DIYSynthMNL/Eurorack-Electric-Druid-VCDO1/kicad/Eurorack_Electric_Druid_VCDO1_Control_Board.kicad_sch

## KiCad design kicad/Eurorack_Electric_Druid_VCDO1_Control_Board.kicad_sch (2025-03-11, an earlier design)

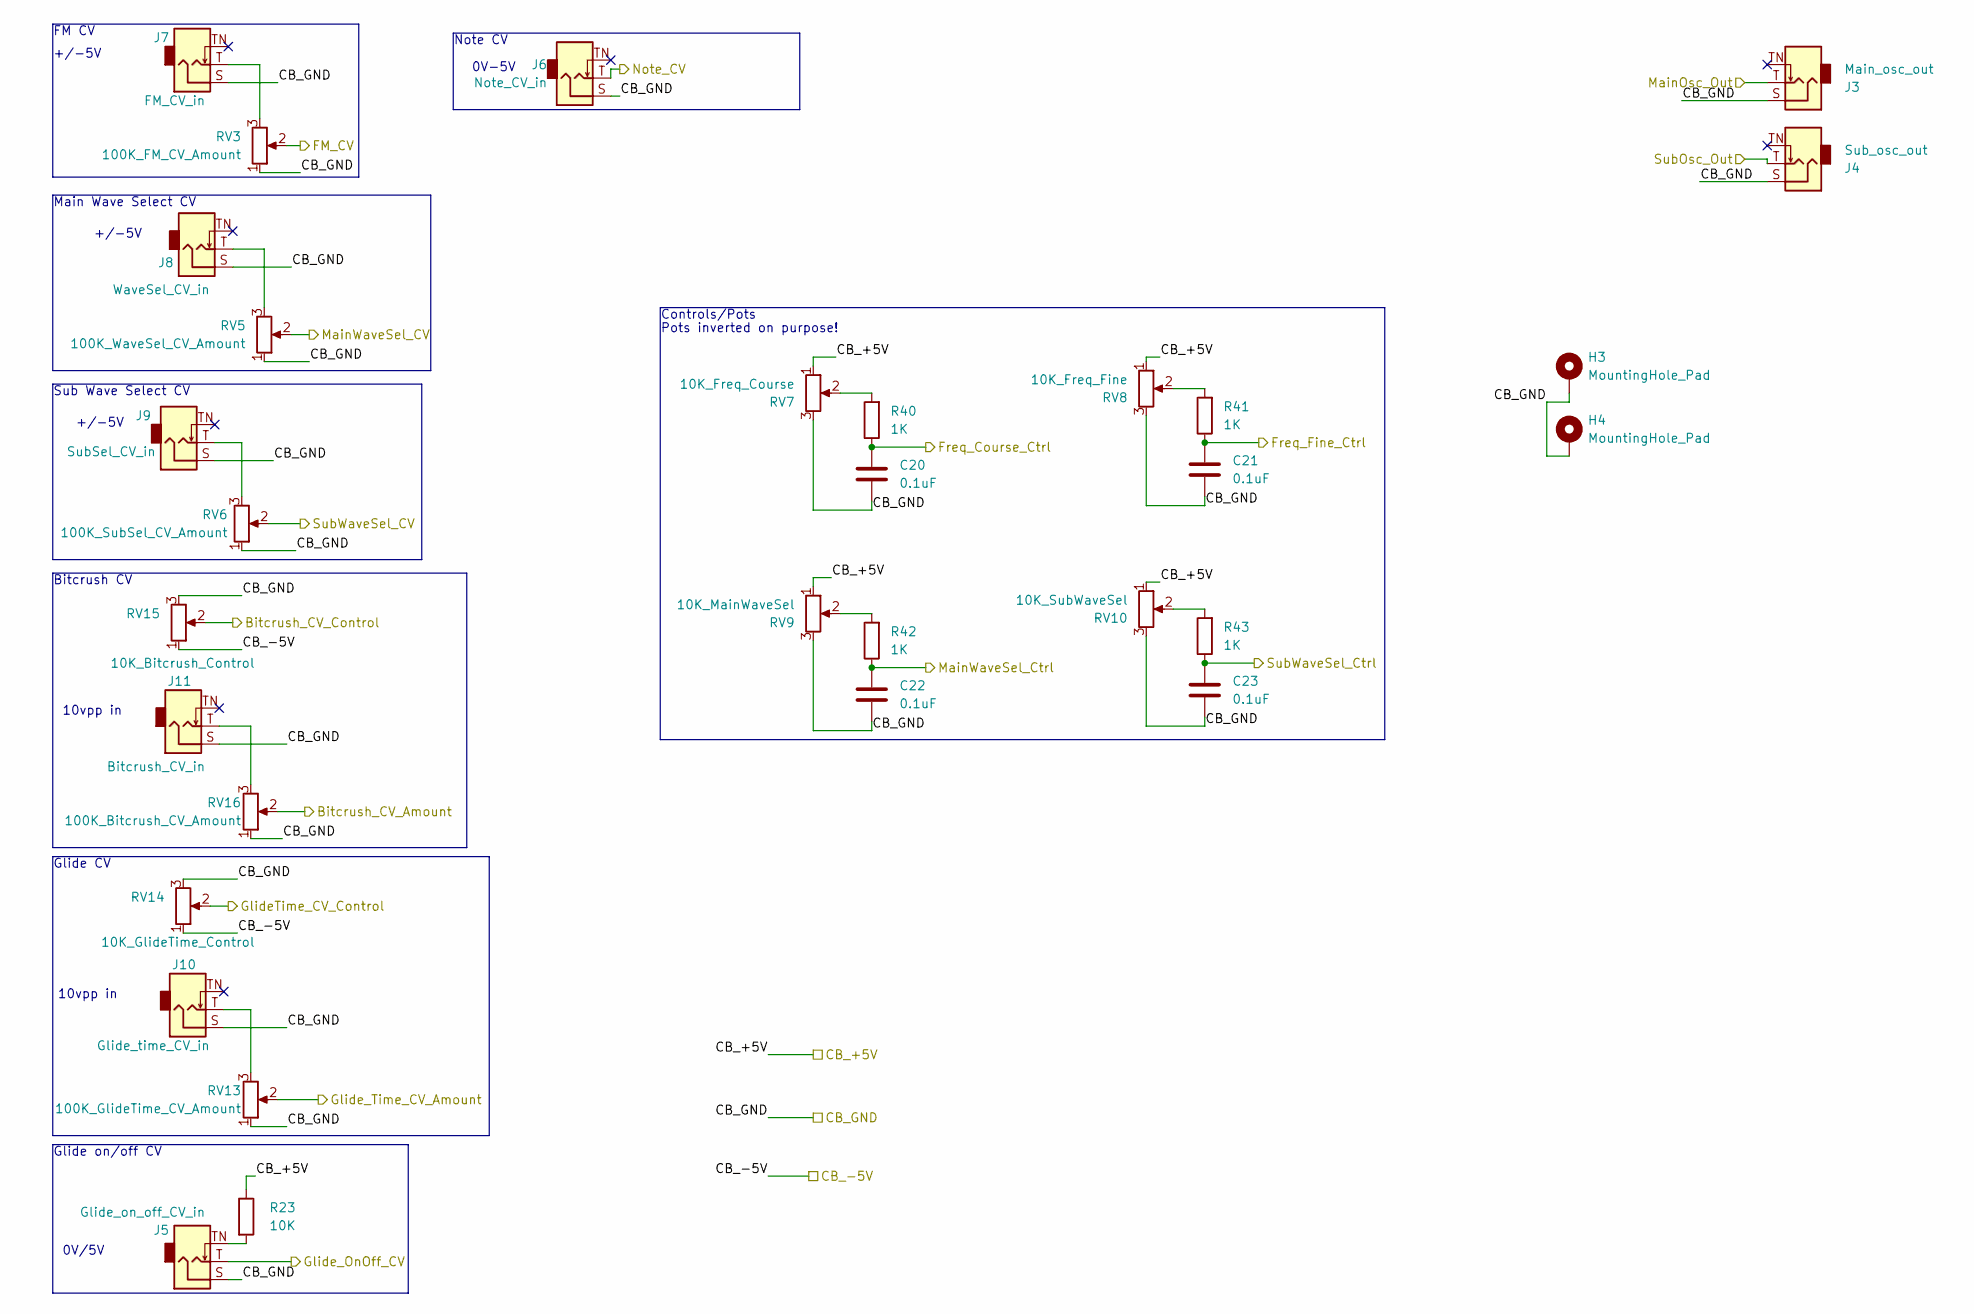
[picture p33: schematic Eurorack_Electric_Druid_VCDO1_Control_Board.kicad_sch]

Parts:
C20, C21, C22, C23: 0.1uF; C_Rect_L7.0mm_W2.0mm_P5.00mm_BigPads
H3, H4: MountingHole_Pad; MountingHole_M3_Standoff_Pad
J3: Main_osc_out; AudioJack_3.5mm_long_pads
J4: Sub_osc_out; AudioJack_3.5mm_long_pads
J5: Glide_on_off_CV_in; AudioJack_3.5mm_long_pads
J6: Note_CV_in; AudioJack_3.5mm_long_pads
J7: FM_CV_in; AudioJack_3.5mm_long_pads
J8: WaveSel_CV_in; AudioJack_3.5mm_long_pads
J9: SubSel_CV_in; AudioJack_3.5mm_long_pads
J10: Glide_time_CV_in; AudioJack_3.5mm_long_pads
J11: Bitcrush_CV_in; AudioJack_3.5mm_long_pads
R23: 10K; R_quarter_watt_L6.3mm_D2.5mm_P7.62mm
R40, R41, R42, R43: 1K; R_quarter_watt_L6.3mm_D2.5mm_P7.62mm
RV3: 100K_FM_CV_Amount; Potentiometer_RV09_BigPads
RV5: 100K_WaveSel_CV_Amount; Potentiometer_RV09_BigPads
RV6: 100K_SubSel_CV_Amount; Potentiometer_RV09_BigPads
RV7: 10K_Freq_Course; Potentiometer_RV09_BigPads
RV8: 10K_Freq_Fine; Potentiometer_RV09_BigPads
RV9: 10K_MainWaveSel; Potentiometer_RV09_BigPads
RV10: 10K_SubWaveSel; Potentiometer_RV09_BigPads
RV13: 100K_GlideTime_CV_Amount; Potentiometer_RV09_BigPads
RV14: 10K_GlideTime_Control; Potentiometer_RV09_BigPads
RV15: 10K_Bitcrush_Control; Potentiometer_RV09_BigPads
RV16: 100K_Bitcrush_CV_Amount; Potentiometer_RV09_BigPads

Connections:
Bitcrush_CV_Amount: RV16.2
Bitcrush_CV_Control: RV15.2
CB_+5V: R23.1, RV7.1, RV8.1, RV9.1, RV10.1
CB_-5V: RV14.1, RV15.1
CB_GND: C20.2, C21.2, C22.2, C23.2, H3.1, H4.1, J3.S, J4.S, J5.S, J6.S, J7.S, J8.S, J9.S, J10.S, J11.S, RV3.1, RV5.1, RV6.1, RV7.3, RV8.3, RV9.3, RV10.3, RV13.1, RV14.3, RV15.3, RV16.1
FM_CV: RV3.2
Freq_Course_Ctrl: C20.1, R40.1
Freq_Fine_Ctrl: C21.1, R41.1
GlideTime_CV_Control: RV14.2
Glide_OnOff_CV: J5.T
Glide_Time_CV_Amount: RV13.2
MainOsc_Out: J3.T
MainWaveSel_CV: RV5.2
MainWaveSel_Ctrl: C22.1, R42.1
unnamed: J5.TN, R23.2
unnamed: J7.T, RV3.3
unnamed: J8.T, RV5.3
unnamed: J9.T, RV6.3
unnamed: J10.T, RV13.3
unnamed: J11.T, RV16.3
unnamed: R40.2, RV7.2
unnamed: R41.2, RV8.2
unnamed: R42.2, RV9.2
unnamed: R43.2, RV10.2
Note_CV: J6.T
SubOsc_Out: J4.T
SubWaveSel_CV: RV6.2
SubWaveSel_Ctrl: C23.1, R43.1

Notes on the sheet:
10vpp in
+/-5V
0V/5V
Main Wave Select CV
Pots inverted on purpose!
0V-5V
FM CV
Sub Wave Select CV
Glide CV
Bitcrush CV
Note CV
Glide on/off CV
Controls/Pots
