DIYSynthMNL/Eurorack-Electric-Druid-VCDO1/kicad/Eurorack_Electric_Druid_VCDO1_Main_Board.kicad_sch

## KiCad design kicad/Eurorack_Electric_Druid_VCDO1_Main_Board.kicad_sch (2025-03-11, an earlier design)

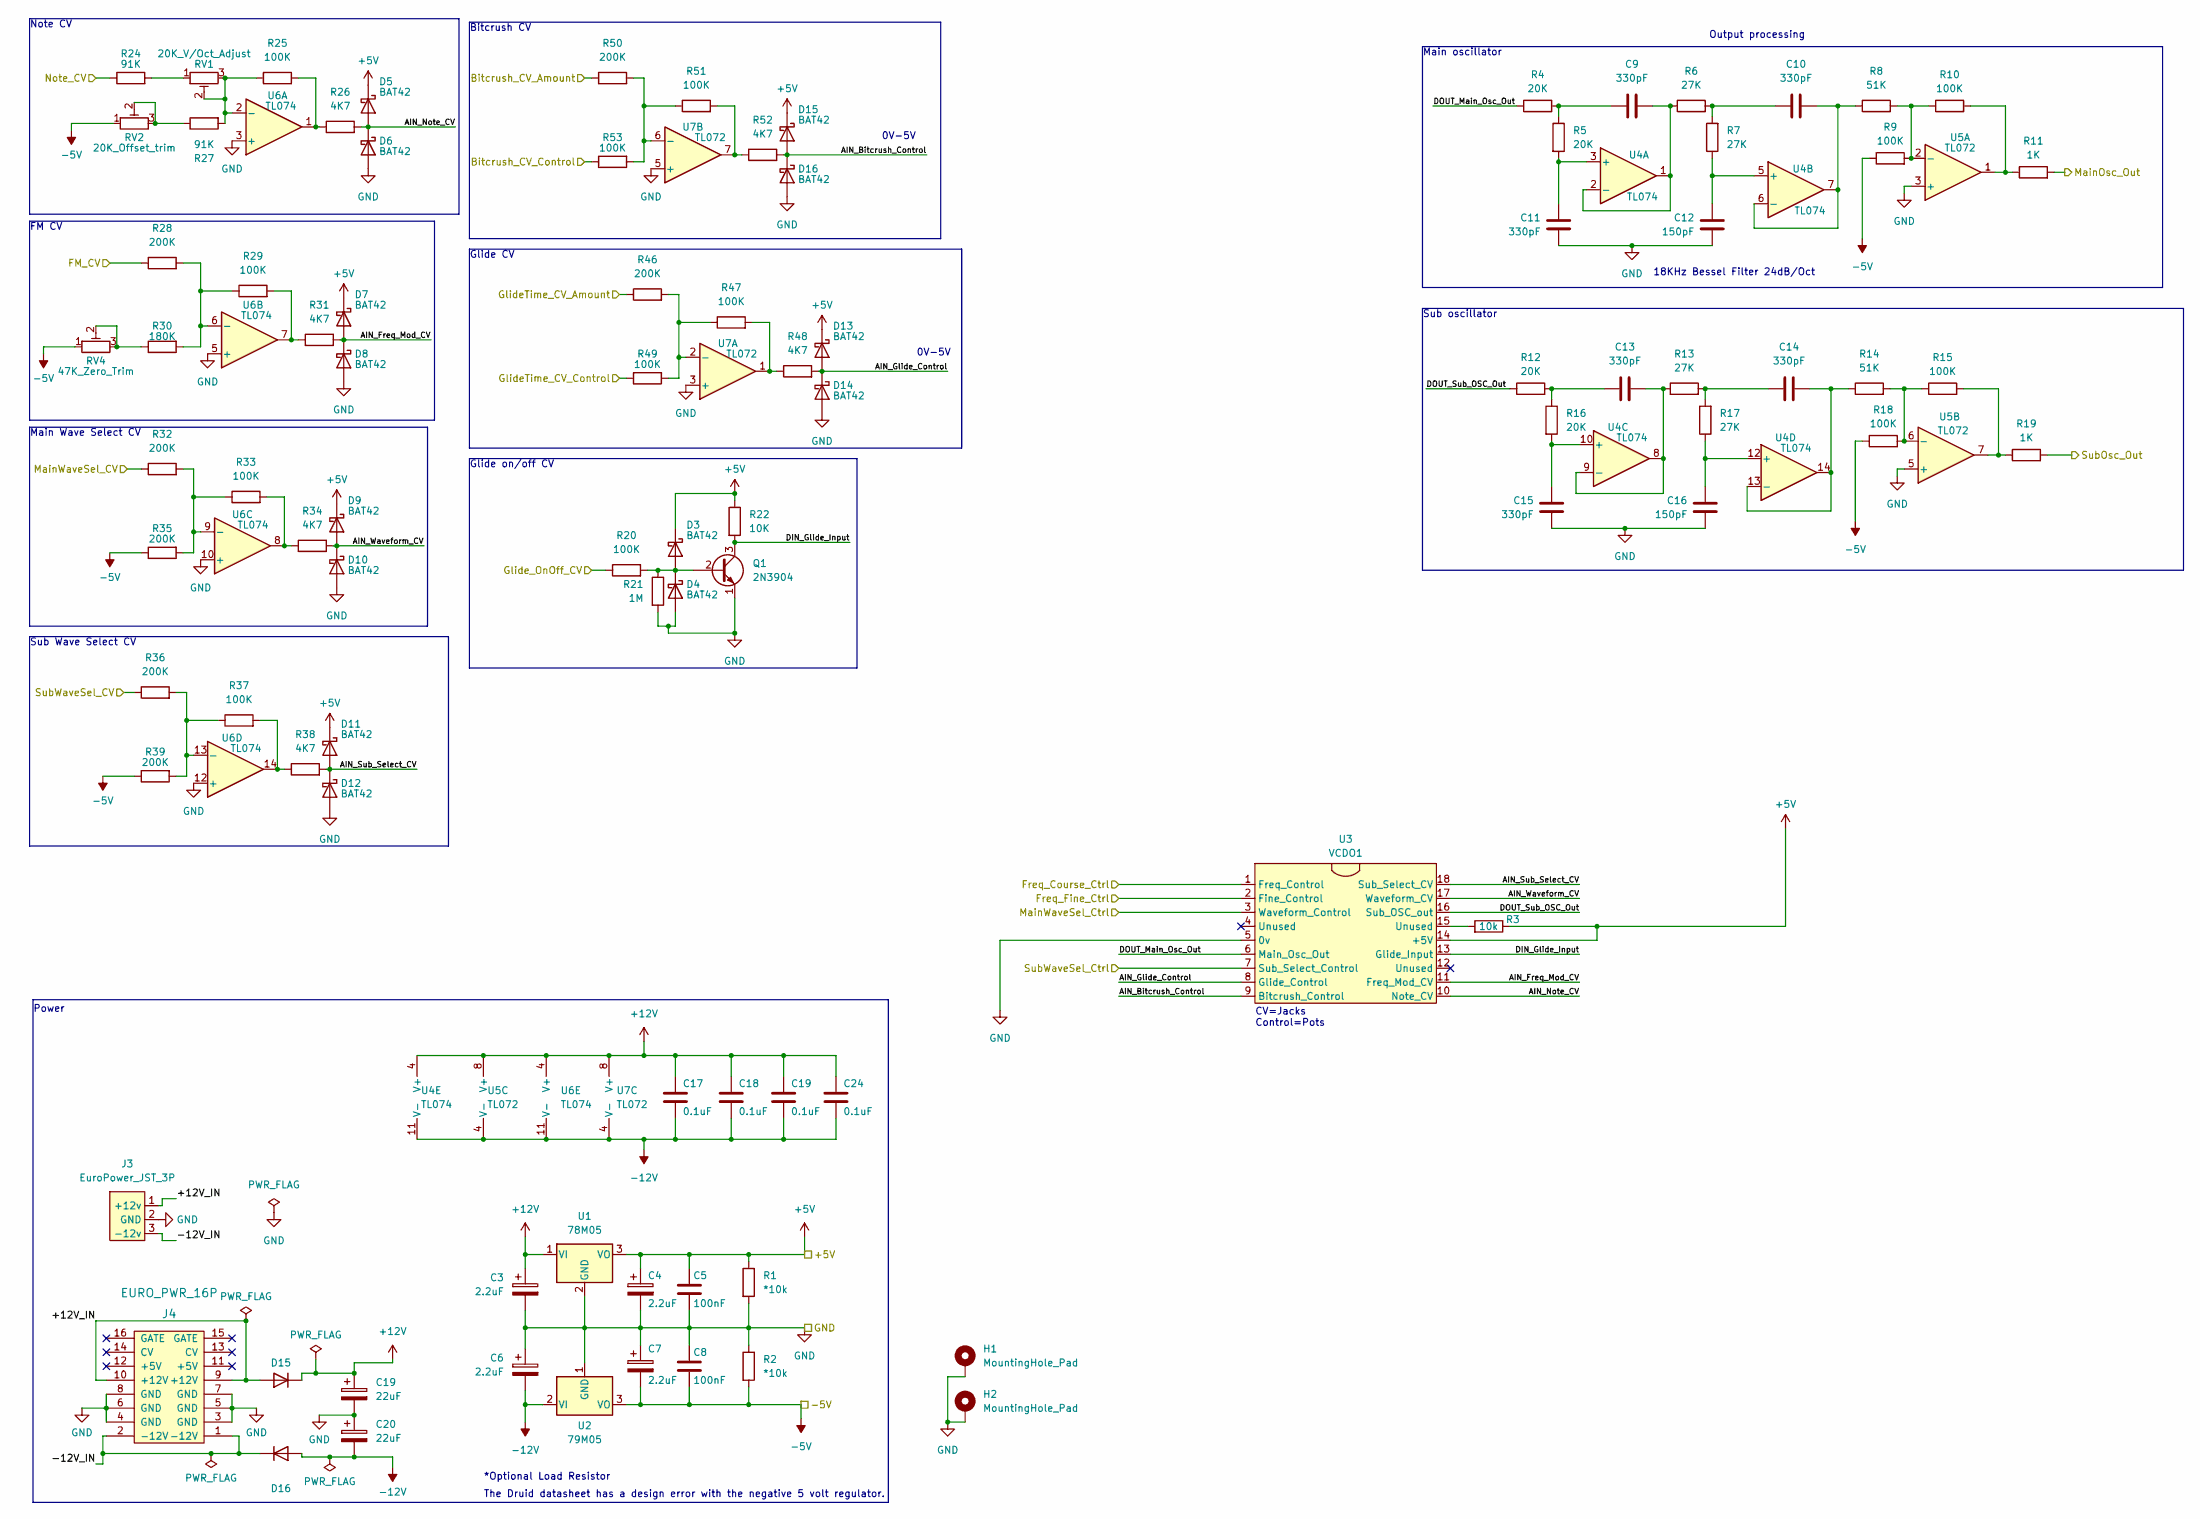
[picture p34: schematic Eurorack_Electric_Druid_VCDO1_Main_Board.kicad_sch]

Parts:
C3, C4, C6, C7: 2.2uF; CP_Radial_D5.0mm_P2.50mm
C5, C8: 100nF; C_Rect_L7.0mm_W2.0mm_P5.00mm_BigPads
C9, C10, C11, C13, C14, C15: 330pF; C_Rect_L7.0mm_W2.0mm_P5.00mm_BigPads
C12, C16: 150pF; C_Rect_L7.0mm_W2.0mm_P5.00mm_BigPads
C17, C18, C19, C24: 0.1uF; C_Rect_L7.0mm_W2.0mm_P5.00mm_BigPads
C20: 22uF; CP_Radial_D4.0mm_P1.50mm
D3, D4, D5, D6, D7, D8, D9, D10, D11, D12, D13, D14, D15: BAT42; D_DO-35_SOD27_P7.62mm_Horizontal
D16: D_DO-41_SOD81_P7.62mm_Horizontal_BigPads
H1, H2: MountingHole_Pad; MountingHole_M3_Standoff_Pad
J3: EuroPower_JST_3P; Eurorack_power_jst_3P
J4: EURO_PWR_16P; IDC-Header_2x08_P2.54mm_Vertical
Q1: 2N3904; TO-92_Inline
R1, R2: *10k; R_quarter_watt_L6.3mm_D2.5mm_P7.62mm
R3: 10k; R_quarter_watt_L6.3mm_D2.5mm_P7.62mm
R4, R5, R12, R16: 20K; R_quarter_watt_L6.3mm_D2.5mm_P7.62mm
R6, R7, R13, R17: 27K; R_quarter_watt_L6.3mm_D2.5mm_P7.62mm
R8, R14: 51K; R_quarter_watt_L6.3mm_D2.5mm_P7.62mm
R9, R10, R15, R18, R20, R25, R29, R33, R37, R47, R49, R51, R53: 100K; R_quarter_watt_L6.3mm_D2.5mm_P7.62mm
R11, R19: 1K; R_quarter_watt_L6.3mm_D2.5mm_P7.62mm
R21: 1M; R_quarter_watt_L6.3mm_D2.5mm_P7.62mm
R22: 10K; R_quarter_watt_L6.3mm_D2.5mm_P7.62mm
R24, R27: 91K; R_quarter_watt_L6.3mm_D2.5mm_P7.62mm
R26, R31, R34, R38, R48, R52: 4K7; R_quarter_watt_L6.3mm_D2.5mm_P7.62mm
R28, R32, R35, R36, R39, R46, R50: 200K; R_quarter_watt_L6.3mm_D2.5mm_P7.62mm
R30: 180K; R_quarter_watt_L6.3mm_D2.5mm_P7.62mm
RV1: 20K_V/Oct_Adjust; Potentiometer_Bourns_3296W_Vertical_BigPads
RV2: 20K_Offset_trim; Potentiometer_Bourns_3296W_Vertical_BigPads
RV4: 47K_Zero_Trim; Potentiometer_Bourns_3296W_Vertical_BigPads
U1: 78M05; TO-252-2
U2: 79M05; TO-252-2
U3: VCDO1; DIP-18_W7.62mm_LongPads
U4, U6: TL074; DIP-14_W7.62mm_LongPads
U5, U7: TL072; DIP-8_W7.62mm_LongPads

Connections:
+5V: C4.1, C5.1, D3.1 (K), D5.1 (K), D7.1 (K), D9.1 (K), D11.1 (K), D13.1 (K), D15.1 (K), R1.1, R3.1, R22.1, U1.3 (VO), U3.14 (+5V)
+12V: C3.1, C17.1, C18.1, C19.1, C24.1, D15.1 (K), U1.1 (VI), U4.4 (V+), U5.8 (V+), U6.4 (V+), U7.8 (V+)
+12V_IN: D15.2 (A), J3.1 (+12v), J4.9 (+12V), J4.10 (+12V)
-5V: C7.2, C8.2, R2.2, R9.1, R18.1, R35.1, R39.1, RV2.1, RV4.1, U2.3 (VO)
-12V: C6.2, C17.2, C18.2, C19.2, C20.2, C24.2, D16.2 (A), U2.2 (VI), U4.11 (V-), U5.4 (V-), U6.11 (V-), U7.4 (V-)
-12V_IN: D16.1 (K), J3.3 (-12v), J4.1 (-12V), J4.2 (-12V)
AIN_Bitcrush_Control: D15.2 (A), D16.1 (K), R52.2, U3.9 (Bitcrush_Control)
AIN_Freq_Mod_CV: D7.2 (A), D8.1 (K), R31.2, U3.11 (Freq_Mod_CV)
AIN_Glide_Control: D13.2 (A), D14.1 (K), R48.2, U3.8 (Glide_Control)
AIN_Note_CV: D5.2 (A), D6.1 (K), R26.2, U3.10 (Note_CV)
AIN_Sub_Select_CV: D11.2 (A), D12.1 (K), R38.2, U3.18 (Sub_Select_CV)
AIN_Waveform_CV: D9.2 (A), D10.1 (K), R34.2, U3.17 (Waveform_CV)
Bitcrush_CV_Amount: R50.1
Bitcrush_CV_Control: R53.1
DIN_Glide_Input: Q1.3 (C), R22.2, U3.13 (Glide_Input)
DOUT_Main_Osc_Out: R4.1, U3.6 (Main_Osc_Out)
DOUT_Sub_OSC_Out: R12.1, U3.16 (Sub_OSC_out)
FM_CV: R28.1
Freq_Course_Ctrl: U3.1 (Freq_Control)
Freq_Fine_Ctrl: U3.2 (Fine_Control)
GND: C3.2, C4.2, C5.2, C6.1, C7.1, C8.1, C11.1, C12.1, C15.1, C16.1, C19.2, C20.1, D4.2 (A), D6.2 (A), D8.2 (A), D10.2 (A), D12.2 (A), D14.2 (A), D16.2 (A), H1.1, H2.1, J3.2 (GND), J4.3 (GND), J4.4 (GND), J4.5 (GND), J4.6 (GND), J4.7 (GND), J4.8 (GND), Q1.1 (E), R1.2, R2.1, R21.2, U1.2 (GND), U2.1 (GND), U3.5 (0v), U5.3 (+), U5.5 (+), U6.3 (+), U6.5 (+), U6.10 (+), U6.12 (+), U7.3 (+), U7.5 (+)
GlideTime_CV_Amount: R46.1
GlideTime_CV_Control: R49.1
Glide_OnOff_CV: R20.1
MainOsc_Out: R11.2
MainWaveSel_CV: R32.1
MainWaveSel_Ctrl: U3.3 (Waveform_Control)
unnamed: C9.1, R4.2, R5.1
unnamed: C9.2, R6.1, U4.1, U4.2 (-)
unnamed: C10.1, R6.2, R7.2
unnamed: C10.2, R8.1, U4.6 (-), U4.7
unnamed: C11.2, R5.2, U4.3 (+)
unnamed: C12.2, R7.1, U4.5 (+)
unnamed: C13.1, R12.2, R16.1
unnamed: C13.2, R13.1, U4.8, U4.9 (-)
unnamed: C14.1, R13.2, R17.2
unnamed: C14.2, R14.1, U4.13 (-), U4.14
unnamed: C15.2, R16.2, U4.10 (+)
unnamed: C16.2, R17.1, U4.12 (+)
unnamed: D3.2 (A), D4.1 (K), Q1.2 (B), R20.2, R21.1
unnamed: R3.2, U3.15 (Unused)
unnamed: R8.2, R9.2, R10.1, U5.2 (-)
unnamed: R10.2, R11.1, U5.1
unnamed: R14.2, R15.1, R18.2, U5.6 (-)
unnamed: R15.2, R19.1, U5.7
unnamed: R24.2, RV1.1
unnamed: R25.1, R27.2, RV1.2, RV1.3, U6.2 (-)
unnamed: R25.2, R26.1, U6.1
unnamed: R27.1, RV2.2, RV2.3
unnamed: R28.2, R29.1, R30.2, U6.6 (-)
unnamed: R29.2, R31.1, U6.7
unnamed: R30.1, RV4.2, RV4.3
unnamed: R32.2, R33.1, R35.2, U6.9 (-)
unnamed: R33.2, R34.1, U6.8
unnamed: R36.2, R37.1, R39.2, U6.13 (-)
unnamed: R37.2, R38.1, U6.14
unnamed: R46.2, R47.1, R49.2, U7.2 (-)
unnamed: R47.2, R48.1, U7.1
unnamed: R50.2, R51.1, R53.2, U7.6 (-)
unnamed: R51.2, R52.1, U7.7
Note_CV: R24.1
SubOsc_Out: R19.2
SubWaveSel_CV: R36.1
SubWaveSel_Ctrl: U3.7 (Sub_Select_Control)

Notes on the sheet:
Output processing
*Optional Load Resistor
Glide on/off CV
0V-5V
Power
The Druid datasheet has a design error with the negative 5 volt regulator.
18KHz Bessel Filter 24dB/Oct
FM CV
Glide CV
Sub Wave Select CV
CV=Jacks Control=Pots
Main oscillator
Main Wave Select CV
Sub oscillator
Bitcrush CV
Note CV
